sdjespersen/epworth-organ/src/bin/primary-encoder/usb_midi.rs

/// USB MIDI interface for the Epworth organ.
///
/// Most software supports automatic MIDI mapping ("MIDI learn") these days, but for details, read on.
///
/// The keyboards on the Epworth organ function much like any other non-velocity sensitive MIDI keyboard. The channels
/// are assigned as follows:
/// - Swell = Channel 1
/// - Great = Channel 2
/// - Choir = Channel 3
/// - Pedal = Channel 4
///
/// All keyboards send "note on" and "note off" messages with fixed velocity 64. The three manuals (swell, great, choir)
/// span the key range from MIDI note 36 to MIDI note 96, inclusive. The pedal ranges from 36 to 67 (inclusive).
///
/// The stops map to continuous controllers that were left undefined in the MIDI spec: 102-117. They function as toggle
/// switches; a "stop on" is communicated with value 127 and "stop off" with value 0. The channel assignments are the
/// same as for the keyboards.
///
/// "General cancel" is communicated with NRPN 1 value 127 on channel 5.
///
/// Pressing a piston (recalling a preset) equates to a MIDI program change on channel 5, plus all the resulting stop
/// changes.
///
/// The swell pedal functions as an expression pedal (CC 11) on channel 1.
/// The choir pedal functions as an expression pedal (CC 11) on channel 3.
/// The crescendo pedal functions as an expression pedal (CC 11) on channel 5.
use usbd_midi::message::channel::Channel;
use usbd_midi::{Message, UsbMidiPacketReader};

use crate::Division;

use embassy_rp::{peripherals::USB, usb::Driver};
use embassy_usb::class::midi::{Receiver, Sender};

use epworth_organ::command::Command;
use epworth_organ::event::Event;
use epworth_organ::stops::Stop;

fn div_cc_bufs(stop_state: u64) -> [[u8; 60]; 4] {
    let mut bufs = [[0u8; 60]; 4];
    for div in 0..4 {
        for i in 0..15 {
            let shift = 16 * div + i;
            let midi_val = if stop_state >> shift & 1 == 1 { 127 } else { 0 };
            let start = 4 * i;
            bufs[div][start] = 0x0B;
            bufs[div][start + 1] = div as u8 | 0xB0;
            bufs[div][start + 2] = 102 + i as u8;
            bufs[div][start + 3] = midi_val;
        }
    }
    bufs
}

pub async fn write_event_to_usb<'d>(event: Event, sender: &mut Sender<'d, Driver<'d, USB>>) {
    // Certain events require quite different handling.
    if let Event::PresetRecalled(idx, stop_state) = event {
        let _ = sender.write_packet(&[0x0C, 0xC4, idx, 0x00]).await;
        for buf in div_cc_bufs(stop_state) {
            let _ = sender.write_packet(&buf).await;
        }
    }
    if let Event::GeneralCancel() = event {
        // GC NRPN: Channel 5 (not tied to a particular division), NRPN 0, value 127 to indicate pushed
        let gc_nrpn = [
            0x0B, 0xB4, 0x63, 0x00, 0x0B, 0xB4, 0x62, 0x01, 0x0B, 0xB4, 0x06, 0x7F,
        ];
        let _ = sender.write_packet(&gc_nrpn).await;
        // Send MIDI events to turn all stops off.
        for buf in div_cc_bufs(0) {
            let _ = sender.write_packet(&buf).await;
        }
    }
    // The rest of the events map to a single 4-byte packet and have uniform handling.
    let some_packet = match event {
        Event::NoteOff(div, note) => Some([0x08, div as u8 | 0x80, note + 36, 0x80]),
        Event::NoteOn(div, note) => Some([0x08, div as u8 | 0x90, note + 36, 0x80]),
        Event::StopOff(stop) => Some([0x0B, stop.div() as u8 | 0xB0, 102 + stop.idx(), 0x00]),
        Event::StopOn(stop) => Some([0x0B, stop.div() as u8 | 0xB0, 102 + stop.idx(), 0x7F]),
        Event::Expression(div, value) => Some([0x0B, div as u8 | 0xB0, 0x0B, value]),
        Event::Crescendo(value) => Some([0x0B, 0xB4, 0x0B, value]),
        Event::PresetRecalled(_, _) => None, // already handled above
        Event::GeneralCancel() => None,      // already handled above
    };
    if let Some(packet) = some_packet {
        let _ = sender.write_packet(&packet).await;
    }
}

fn div_from_channel(channel: Channel) -> Option<Division> {
    match channel {
        Channel::Channel1 => Some(Division::Swell),
        Channel::Channel2 => Some(Division::Great),
        Channel::Channel3 => Some(Division::Choir),
        Channel::Channel4 => Some(Division::Pedal),
        _ => None,
    }
}

fn midi_message_to_command(message: Message) -> Option<Command> {
    match message {
        Message::NoteOff(channel, note, _) => {
            let note_val: u8 = note.into();
            if let Some(div) = div_from_channel(channel) {
                Some(Command::NoteOff(div, note_val - 36))
            } else {
                None
            }
        }
        Message::NoteOn(channel, note, _) => {
            let note_val: u8 = note.into();
            if let Some(div) = div_from_channel(channel) {
                Some(Command::NoteOn(div, note_val - 36))
            } else {
                None
            }
        }
        Message::ControlChange(channel, control_fn, value) => {
            // between 102-117, stop changes
            let controller: u8 = control_fn.0.into();
            let some_div = div_from_channel(channel);
            if 102 <= controller
                && controller <= 117
                && let Some(div) = some_div
            {
                let stop = Stop::try_from(div, controller - 102);
                if let Some(s) = stop {
                    if u8::from(value) < 64 {
                        Some(Command::StopOff(s))
                    } else {
                        Some(Command::StopOn(s))
                    }
                } else {
                    None
                }
            } else if controller == 11 {
                if channel == Channel::Channel5 {
                    Some(Command::Crescendo(value.into()))
                } else if let Some(div) = some_div {
                    Some(Command::Expression(div, value.into()))
                } else {
                    None
                }
            } else {
                None
            }
        }
        Message::Reset => Some(Command::GeneralCancel()),
        _ => None,
    }
}

pub async fn receive_command_from_usb<'d>(
    data: &mut [u8; 64],
    receiver: &mut Receiver<'d, Driver<'d, USB>>,
    mut handle_cmd: impl AsyncFnMut(Command),
) {
    match receiver.read_packet(data).await {
        Ok(n) if n > 0 => {
            let packet_reader = UsbMidiPacketReader::new(&data, n);
            for packet in packet_reader.into_iter() {
                if let Ok(packet) = packet {
                    if let Ok(message) = Message::try_from(&packet) {
                        if let Some(cmd) = midi_message_to_command(message) {
                            handle_cmd(cmd).await;
                        }
                    }
                }
            }
        }
        Err(e) => {
            defmt::error!("Error reading from USB: {:?}", e);
        }
        Ok(_) => {}
    };
}
