sdjespersen/epworth-organ/src/command.rs

use crate::stops::Stop;
use serde::{Deserialize, Serialize};

use crate::Division;

pub enum CommandSource {
    External,
    Local,
}

#[derive(Serialize, Deserialize)]
pub enum Command {
    NoteOff(Division, u8),
    NoteOn(Division, u8),
    StopOff(Stop),
    StopOn(Stop),
    StopToggle(Stop),
    RecallPreset(u8),
    GeneralCancel(),
    EnableSave(bool),
    Expression(Division, u8),
    Crescendo(u8),
}
